ArcadiaLabs/balancing_robot/STL/tool_wrench.stl

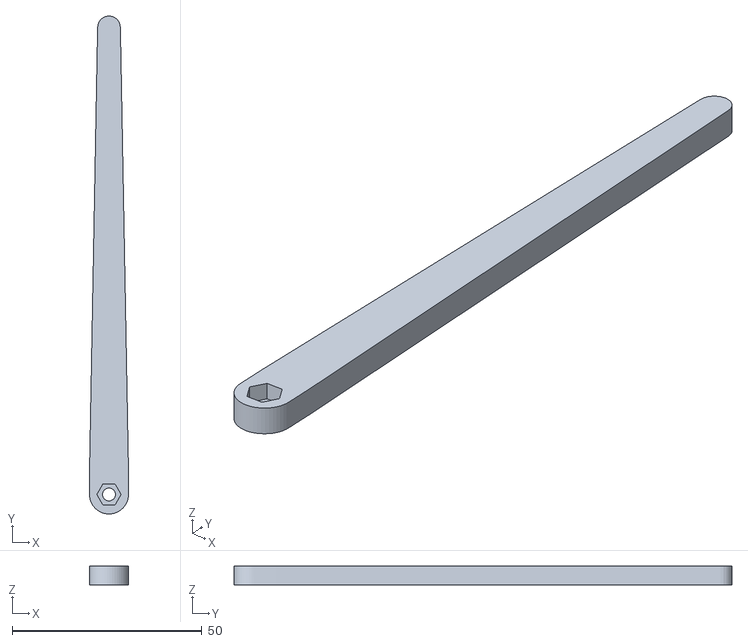
[picture p18: CAD file, 2017-07-10]
STL/tool_wrench.stl
10.3 x 131.1 x 5.00
