ArcadiaLabs/balancing_robot/STL/servo_holder_part1.stl

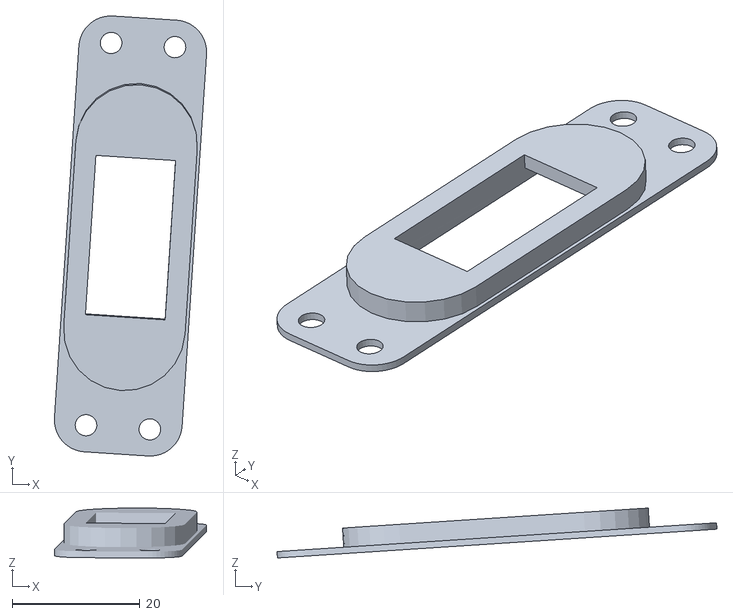
[picture p19: CAD file, 2017-07-10]
STL/servo_holder_part1.stl
23.8 x 68.8 x 7.81
