ArcadiaLabs/balancing_robot/STL/tray_small.stl

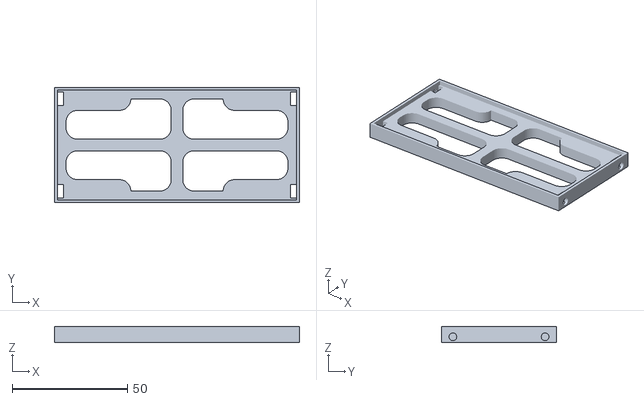
[picture p20: CAD file, 2017-07-10]
STL/tray_small.stl
106.2 x 50.0 x 7.00
