ArcadiaLabs/balancing_robot/STL/bumper1_leds_strip.stl

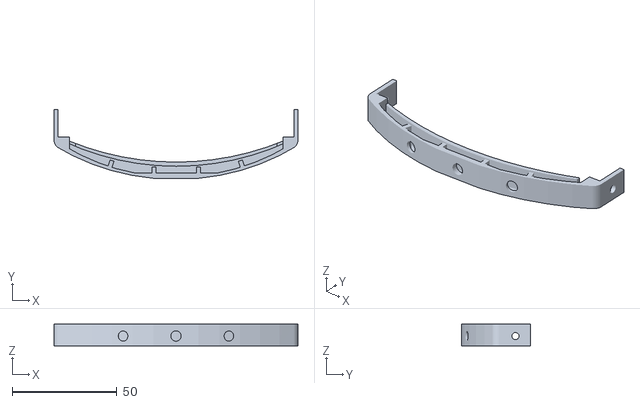
[picture p21: CAD file, 2017-07-10]
STL/bumper1_leds_strip.stl
116.4 x 32.7 x 10.4
